jcranney/smart-switch/electronic/rocker/led_circuit.asc

C1: cap; 50µ
D1: LED
D2: LED
R1: res; 3.3k
R2: res; 3.3k
R3: res; 880
R4: res; 3.3k
R5: res; 880
R6: res; 880
R7: res; 880
R8: res; 880
U1: OP07
U2: OP07
U3: OP07
U4: OP07
V1: voltage; 5
V2: voltage; 2
Named nets: 0, VCC, Vin, VWP, VWM
;.ac list

;.dc V2 0 5 0.01
.tran 0 0.01 0 0.001 startup
